gmtii/Prototipo-R820T2/r820t2/r820t_lib.ino

#define R820T2_I2C_ADDRESS   (0x1A)
#define I2C_DEBUG
/*
   Freq calcs
*/
#define XTAL_FREQ           25000000
#define IF_FREQ             5000000
#define CALIBRATION_LO      88000


uint32_t  r820t_freq   =   126200000;
//uint32_t  r820t_freq   =   739900000; // para qo100


#define R820T2_WRITE_START  5
#define R820T2_NUM_REGS 0x20
#define BUFFER_LENGTH 32

/* initial values from airspy */
/* initial freq @ 128MHz -> ~5MHz IF due to xtal mismatch */
static const uint8_t regs_init_array[R820T2_NUM_REGS] = {
  0x00, 0x00, 0x00, 0x00, 0x00,   /* 00 to 04 */
  /* 05 */ 0x90, // LNA manual gain mode, init to 0
  /* 06 */ 0x80,
  /* 07 */ 0x60,
  /* 08 */ 0x80, // Image Gain Adjustment
  /* 09 */ 0x40, // Image Phase Adjustment
  /* 0A */ 0xA8, // Channel filter [0..3]: 0 = widest, f = narrowest - Optimal. Don't touch!
  /* 0B */ 0x0F, // High pass filter - Optimal. Don't touch!
  /* 0C */ 0x40, // VGA control by code, init at 0
  /* 0D */ 0x63, // LNA AGC settings: [0..3]: Lower threshold; [4..7]: High threshold
  /* 0E */ 0x75,
  /* 0F */ 0x68, // Filter Widest, LDO_5V OFF, clk out ON,
  /* 10 */ 0x7C, // REFDIV = 0
  /* 11 */ 0x83,
  /* 12 */ 0x80,
  /* 13 */ 0x00,
  /* 14 */ 0x0F,
  /* 15 */ 0x00,
  /* 16 */ 0xC0,
  /* 17 */ 0x30,
  /* 18 */ 0x48,
  /* 19 */ 0xCC,
  /* 1A */ 0x60,
  /* 1B */ 0x00,
  /* 1C */ 0x54,
  /* 1D */ 0xAE,
  /* 1E */ 0x0A,
  /* 1F */ 0xC0
};

#define ARRAY_SIZE(arr) (sizeof(arr) / sizeof((arr)[0]))

/*
   Tuner frequency ranges
   Kanged & modified from airspy firmware to include freq for scanning table
   "Copyright (C) 2013 Mauro Carvalho Chehab"
   https://stuff.mit.edu/afs/sipb/contrib/linux/drivers/media/tuners/r820t.c
*/
struct r820t2_freq_range {
  uint16_t freq;
  uint8_t open_d;
  uint8_t rf_mux_ploy;
  uint8_t tf_c;
};
const struct r820t2_freq_range freq_ranges[] = {
  {
    /* 0 MHz */              0,
    /* .open_d = */       0x08, /* low */
    /* .rf_mux_ploy = */  0x02, /* R26[7:6]=0 (LPF)  R26[1:0]=2 (low) */
    /* .tf_c = */         0xDF, /* R27[7:0]  band2,band0 */
  }, {
    /* 50 MHz */            50,
    /* .open_d = */       0x08, /* low */
    /* .rf_mux_ploy = */  0x02, /* R26[7:6]=0 (LPF)  R26[1:0]=2 (low) */
    /* .tf_c = */         0xBE, /* R27[7:0]  band4,band1  */
  }, {
    /* 55 MHz */            55,
    /* .open_d = */       0x08, /* low */
    /* .rf_mux_ploy = */  0x02, /* R26[7:6]=0 (LPF)  R26[1:0]=2 (low) */
    /* .tf_c = */         0x8B, /* R27[7:0]  band7,band4 */
  }, {
    /* 60 MHz */            60,
    /* .open_d = */       0x08, /* low */
    /* .rf_mux_ploy = */  0x02, /* R26[7:6]=0 (LPF)  R26[1:0]=2 (low) */
    /* .tf_c = */         0x7B, /* R27[7:0]  band8,band4 */
  }, {
    /* 65 MHz */            65,
    /* .open_d = */       0x08, /* low */
    /* .rf_mux_ploy = */  0x02, /* R26[7:6]=0 (LPF)  R26[1:0]=2 (low) */
    /* .tf_c = */         0x69, /* R27[7:0]  band9,band6 */
  }, {
    /* 70 MHz */            70,
    /* .open_d = */       0x08, /* low */
    /* .rf_mux_ploy = */  0x02, /* R26[7:6]=0 (LPF)  R26[1:0]=2 (low) */
    /* .tf_c = */         0x58, /* R27[7:0]  band10,band7 */
  }, {
    /* 75 MHz */            75,
    /* .open_d = */       0x00, /* high */
    /* .rf_mux_ploy = */  0x02, /* R26[7:6]=0 (LPF)  R26[1:0]=2 (low) */
    /* .tf_c = */         0x44, /* R27[7:0]  band11,band11 */
  }, {
    /* 80 MHz */            80,
    /* .open_d = */       0x00, /* high */
    /* .rf_mux_ploy = */  0x02, /* R26[7:6]=0 (LPF)  R26[1:0]=2 (low) */
    /* .tf_c = */         0x44, /* R27[7:0]  band11,band11 */
  }, {
    /* 90 MHz */            90,
    /* .open_d = */       0x00, /* high */
    /* .rf_mux_ploy = */  0x02, /* R26[7:6]=0 (LPF)  R26[1:0]=2 (low) */
    /* .tf_c = */         0x34, /* R27[7:0]  band12,band11 */
  }, {
    /* 100 MHz */          100,
    /* .open_d = */       0x00, /* high */
    /* .rf_mux_ploy = */  0x02, /* R26[7:6]=0 (LPF)  R26[1:0]=2 (low) */
    /* .tf_c = */         0x34, /* R27[7:0]  band12,band11 */
  }, {
    /* 110 MHz */          110,
    /* .open_d = */       0x00, /* high */
    /* .rf_mux_ploy = */  0x02, /* R26[7:6]=0 (LPF)  R26[1:0]=2 (low) */
    /* .tf_c = */         0x24, /* R27[7:0]  band13,band11 */
  }, {
    /* 120 MHz */          120,
    /* .open_d = */       0x00, /* high */
    /* .rf_mux_ploy = */  0x02, /* R26[7:6]=0 (LPF)  R26[1:0]=2 (low) */
    /* .tf_c = */         0x24, /* R27[7:0]  band13,band11 */
  }, {
    /* 140 MHz */          140,
    /* .open_d = */       0x00, /* high */
    /* .rf_mux_ploy = */  0x02, /* R26[7:6]=0 (LPF)  R26[1:0]=2 (low) */
    /* .tf_c = */         0x14, /* R27[7:0]  band14,band11 */
  }, {
    /* 180 MHz */          180,
    /* .open_d = */       0x00, /* high */
    /* .rf_mux_ploy = */  0x02, /* R26[7:6]=0 (LPF)  R26[1:0]=2 (low) */
    /* .tf_c = */         0x13, /* R27[7:0]  band14,band12 */
  }, {
    /* 220 MHz */          220,
    /* .open_d = */       0x00, /* high */
    /* .rf_mux_ploy = */  0x02, /* R26[7:6]=0 (LPF)  R26[1:0]=2 (low) */
    /* .tf_c = */         0x13, /* R27[7:0]  band14,band12 */
  }, {
    /* 250 MHz */          250,
    /* .open_d = */       0x00, /* high */
    /* .rf_mux_ploy = */  0x02, /* R26[7:6]=0 (LPF)  R26[1:0]=2 (low) */
    /* .tf_c = */         0x11, /* R27[7:0]  highest,highest */
  }, {
    /* 280 MHz */          280,
    /* .open_d = */       0x00, /* high */
    /* .rf_mux_ploy = */  0x02, /* R26[7:6]=0 (LPF)  R26[1:0]=2 (low) */
    /* .tf_c = */         0x00, /* R27[7:0]  highest,highest */
  }, {
    /* 310 MHz */          310,
    /* .open_d = */       0x00, /* high */
    /* .rf_mux_ploy = */  0x41, /* R26[7:6]=1 (bypass)  R26[1:0]=1 (middle) */
    /* .tf_c = */         0x00, /* R27[7:0]  highest,highest */
  }, {
    /* 450 MHz */          450,
    /* .open_d = */       0x00, /* high */
    /* .rf_mux_ploy = */  0x41, /* R26[7:6]=1 (bypass)  R26[1:0]=1 (middle) */
    /* .tf_c = */         0x00, /* R27[7:0]  highest,highest */
  }, {
    /* 588 MHz */          588,
    /* .open_d = */       0x00, /* high */
    /* .rf_mux_ploy = */  0x40, /* R26[7:6]=1 (bypass)  R26[1:0]=0 (highest) */
    /* .tf_c = */         0x00, /* R27[7:0]  highest,highest */
  }, {
    /* 650 MHz */          650,
    /* .open_d = */       0x00, /* high */
    /* .rf_mux_ploy = */  0x40, /* R26[7:6]=1 (bypass)  R26[1:0]=0 (highest) */
    /* .tf_c = */         0x00, /* R27[7:0]  highest,highest */
  }
};



// Cached register values are used in R820T2_write_cache_mask
uint8_t regs_cache[R820T2_NUM_REGS];

// Note: apparently R820T2 allows to read only from address 0x00
void R820T2_read(uint8_t addr, uint8_t *data, uint8_t num) {
  static const uint8_t reverse_table[] = {
    0x0, 0x8, 0x4, 0xC, 0x2, 0xA, 0x6, 0xE,
    0x1, 0x9, 0x5, 0xD, 0x3, 0xB, 0x7, 0xF
  };
  uint16_t timeout = 1000;
  int8_t count = 0;
  uint32_t t1 = millis();
#ifdef I2C_DEBUG
  Serial.print("I2C (0x");
  Serial.print(R820T2_I2C_ADDRESS, HEX);
  Serial.print(") reading ");
  Serial.print(num, DEC);
  Serial.print(" bytes from 0x");
  Serial.print(addr, HEX);
  Serial.print("...");
#endif

  // I2C/TWI subsystem uses internal buffer that breaks with large data requests
  // so if user requests more than BUFFER_LENGTH bytes, we have to do it in
  // smaller chunks instead of all at once
  for (uint8_t k = 0; k < num; k += min((int)num, BUFFER_LENGTH)) {
    Wire.beginTransmission(R820T2_I2C_ADDRESS);
    Wire.write(addr);
    Wire.endTransmission();
    Wire.beginTransmission(R820T2_I2C_ADDRESS);
    Wire.requestFrom(R820T2_I2C_ADDRESS, (uint8_t)min(num - k, BUFFER_LENGTH));

    for (; Wire.available() && (timeout == 0 || millis() - t1 < timeout); count++) {
      data[count] = Wire.read();
#ifdef I2C_DEBUG
      Serial.print(data[count], HEX);
      if (count + 1 < num) Serial.print(" ");
#endif

      // During reading bits are transfered in reverse order,
      // thus we have to restore original bit order.
      for (uint16_t i = 0; i < num; i++) {
        uint16_t val = data[i];
        data[i] = (reverse_table[val & 0xF] << 4) | reverse_table[val >> 4];
      }
    }
    // check for timeout
    if (timeout > 0 && millis() - t1 >= timeout && count < num) count = -1; // timeout

#ifdef I2C_DEBUG
    Serial.print(". Done (");
    Serial.print(count, DEC);
    Serial.println(" read).");
#endif

    //return count;

  }
}
void R820T2_write(uint8_t addr, uint8_t *data, uint8_t num) {
#ifdef I2C_DEBUG
  Serial.print("I2C (0x");
  Serial.print(R820T2_I2C_ADDRESS, HEX);
  Serial.print(") writing ");
  Serial.print(num, DEC);
  Serial.print(" bytes to 0x");
  Serial.print(addr, HEX);
  Serial.print("...");
#endif
  uint8_t status = 0;
  Wire.beginTransmission(R820T2_I2C_ADDRESS);
  Wire.write((uint8_t) addr);
  for (uint8_t i = 0; i < num; i++) {
    Wire.write((uint8_t) data[i]);
#ifdef I2C_DEBUG
    Serial.print(data[i], HEX);
    if (i + 1 < num) Serial.print(" ");
#endif
  }
  status = Wire.endTransmission();
#ifdef I2C_DEBUG
  Serial.print(". Done.");
  Serial.print(". Status = ");
  Serial.println(status);
#endif
  //return status == 0;
}

uint8_t R820T2_read_reg(uint8_t n) {
  if (n >= R820T2_NUM_REGS)
    return 0;

  uint8_t regs[R820T2_NUM_REGS];
  R820T2_read(0x00, regs, sizeof(regs));
  return regs[n];
}

void R820T2_write_reg(uint8_t n, uint8_t data) {
  if (n >= R820T2_NUM_REGS)
    return;
  regs_cache[n] = data;
  R820T2_write(n, &regs_cache[n], 1);
}

/*
   Write single R820T2 reg via I2C with mask vs cached
*/
void R820T2_write_cache_mask(uint8_t reg, uint8_t data, uint8_t mask) {
  /* check for legal reg */
  if (reg >= R820T2_NUM_REGS)
    return;

  /* mask vs cached reg */
  data = (data & mask) | (regs_cache[reg] & ~mask);
  regs_cache[reg] = data;

  /* send via I2C */
  R820T2_write(reg, &regs_cache[reg], 1);
}

/*
   Update Tracking Filter
   Kanged & Modified from airspy firmware

   "inspired by Mauro Carvalho Chehab set_mux technique"
   https://stuff.mit.edu/afs/sipb/contrib/linux/drivers/media/tuners/r820t.c
   part of r820t_set_mux() (set tracking filter)
*/
static void R820T2_set_tf(uint32_t freq) {
  const struct r820t2_freq_range *range;
  unsigned int i;

  /* Get Freq in MHz */
  freq = (uint32_t)((uint64_t)freq * 4295 >> 32); // fast approach

  /* Scan array for proper range */
  for (i = 0; i < ARRAY_SIZE(freq_ranges) - 1; i++) {
    if (freq < freq_ranges[i + 1].freq)

      break;

  }

  range = &freq_ranges[i];
  /* Open Drain */
  R820T2_write_cache_mask(0x17, range->open_d, 0x08);

  /* RF_MUX,Polymux */
  R820T2_write_cache_mask(0x1A, range->rf_mux_ploy, 0xC3);

  /* TF BAND */
  R820T2_write_reg(0x1B, range->tf_c);

  /* XTAL CAP & Drive */
  R820T2_write_cache_mask(0x10, 0x08, 0x0b);

  R820T2_write_cache_mask(0x08, 0x00, 0x3F);

  R820T2_write_cache_mask(0x09, 0x00, 0x3F);
}

/*
   Update LO PLL
*/
void R820T2_set_pll(uint32_t freq) {
  const uint32_t vco_min = 1760000000;
  const uint32_t vco_max = 3900000000;
  uint32_t pll_ref = (XTAL_FREQ >> 1);
  uint32_t pll_ref_2x = XTAL_FREQ;

  uint32_t vco_exact;
  uint32_t vco_frac;
  uint32_t con_frac;
  uint32_t div_num;
  uint32_t n_sdm;
  uint16_t sdm;
  uint8_t ni;
  uint8_t si;
  uint8_t nint;

  /* Calculate VCO output divider */
  for (div_num = 0; div_num < 5; div_num++) {
    vco_exact = freq << (div_num + 1);
    if (vco_exact >= vco_min && vco_exact <= vco_max) {
      break;
    }
  }

  /* Calculate the integer PLL feedback divider */
  vco_exact = freq << (div_num + 1);
  nint = (uint8_t) ((vco_exact + (pll_ref >> 16)) / pll_ref_2x);
  vco_frac = vco_exact - pll_ref_2x * nint;

  nint -= 13;
  ni = (nint >> 2);
  si = nint - (ni << 2);

  /* Set the vco output divider */
  R820T2_write_cache_mask(0x10, (uint8_t) (div_num << 5), 0xE0);

  /* Set the PLL Feedback integer divider */
  R820T2_write_reg(0x14, (uint8_t) (ni + (si << 6)));

  /* Update Fractional PLL */
  if (vco_frac == 0) {
    /* Disable frac pll */
    R820T2_write_cache_mask(0x12, 0x08, 0x08);
  } else {
    /* Compute the Sigma-Delta Modulator */
    vco_frac += pll_ref >> 16;
    sdm = 0;
    for (n_sdm = 0; n_sdm < 16; n_sdm++) {
      con_frac = pll_ref >> n_sdm;
      if (vco_frac >= con_frac) {
        sdm |= (uint16_t) (0x8000 >> n_sdm);
        vco_frac -= con_frac;
        if (vco_frac == 0)
          break;
      }
    }

    /* Update Sigma-Delta Modulator */
    R820T2_write_reg(0x15, (uint8_t)(sdm & 0xFF));
    R820T2_write_reg(0x16, (uint8_t)(sdm >> 8));

    /* Enable frac pll */
    R820T2_write_cache_mask(0x12, 0x00, 0x08);
  }
}

/*
   Update Tracking Filter and LO to frequency
*/
void R820T2_set_frequency(uint32_t freq) {
  r820t_freq = freq;//update frequency cat
  R820T2_set_tf(freq);
  R820T2_set_pll(freq + IF_FREQ);
}

/*
   Set IF Bandwidth [0-15]
*/
void R820T2_set_bandwidth(uint8_t bw) {
  //  const uint8_t modes[] = { 0xE0, 0x80, 0x60, 0x00 };
  //  uint8_t a = 0xB0 | (0x0F - (bw & 0x0F));
  //  uint8_t b = 0x0F | modes[(bw & 0x3) >> 4];
  //  R820T2_write_reg(0x0A, a);
  //  R820T2_write_reg(0x0B, b);

  const uint8_t modes[] = { 0xE0, 0x80, 0x60, 0x00 };
  const uint8_t opt[] = { 15, 14, 13, 12, 11, 10, 9, 8, 7, 6, 5, 4, 3, 2, 1, 0 };
  uint8_t a = 0xB0 | opt[bw & 0x0F];
  uint8_t b = 0x0F | modes[bw >> 4];
  R820T2_write_reg(0x0A, a);
  R820T2_write_reg(0x0B, b);
}

/*
   Set gain of LNA [0-15]
*/
void R820T2_set_lna_gain(uint8_t gain_index) {
  R820T2_write_cache_mask(0x05, gain_index, 0x0F);
}

/*
   Set gain of mixer [0-15]
*/
void R820T2_set_mixer_gain(uint8_t gain_index) {
  R820T2_write_cache_mask(0x07, gain_index, 0x0F);
}

/*
   Set gain of VGA [0-15]
*/
void R820T2_set_vga_gain(uint8_t gain_index) {
  R820T2_write_cache_mask(0x0C, gain_index, 0x0F);
}

/*
   Enable/Disable LNA AGC [0 / 1]
*/
void R820T2_set_lna_agc(uint8_t value) {
  value = value != 0 ? 0x00 : 0x10;
  R820T2_write_cache_mask(0x05, value, 0x10);
}

/*
   Enable/Disable Mixer AGC [0 / 1]
*/
void R820T2_set_mixer_agc(uint8_t value) {
  value = value != 0 ? 0x10 : 0x00;
  R820T2_write_cache_mask(0x07, value, 0x10);
}

/*
   Calibrate
   Kanged from airspy firmware
   "inspired by Mauro Carvalho Chehab calibration technique"
   https://stuff.mit.edu/afs/sipb/contrib/linux/drivers/media/tuners/r820t.c
*/

int32_t R820T2_calibrate() {
  int32_t i, cal_code;

  for (i = 0; i < 5; i++) {
    /* Set filt_cap */
    R820T2_write_cache_mask(0x0B, 0x08, 0x60);

    /* set cali clk =on */
    R820T2_write_cache_mask(0x0F, 0x04, 0x04);

    /* X'tal cap 0pF for PLL */
    R820T2_write_cache_mask(0x10, 0x00, 0x03);

    /* freq used for calibration */
    R820T2_set_pll(CALIBRATION_LO * 1000);

    /* Start Trigger */
    R820T2_write_cache_mask(0x0B, 0x10, 0x10);

    delay(2);

    /* Stop Trigger */
    R820T2_write_cache_mask(0x0B, 0x00, 0x10);

    /* set cali clk =off */
    R820T2_write_cache_mask(0x0F, 0x00, 0x04);

    /* Check if calibration worked */
    cal_code = R820T2_read_reg(0x04) & 0x0F;
    if (cal_code && cal_code != 0x0F)
      return 0;
  }

  /* cal failed */
  return -1;

}

int r820t_standby(void)
{
  R820T2_write_reg(0x05, 0xA0);
  R820T2_write_reg(0x06, 0xD0);
  R820T2_write_reg(0x07, 0x00);
  R820T2_write_reg(0x08, 0x40);
  R820T2_write_reg(0x09, 0xC0);
  R820T2_write_reg(0x0a, 0x70);
  R820T2_write_reg(0x0c, 0xA0);
  R820T2_write_reg(0x0f, 0x2A);
  R820T2_write_reg(0x11, 0x03);
  R820T2_write_reg(0x17, 0xF4);
  R820T2_write_reg(0x19, 0x0C);

  return 0;
}

/*
   Initialize the R820T2
*/
void R820T2_init() {

  byte error;

  Wire.beginTransmission(R820T2_I2C_ADDRESS);
  error = Wire.endTransmission();

  if (error == 0)
  {
    //u8x8.setCursor(0, 5);
    //u8x8.print("OK! R820T found!");

    for (uint8_t i = R820T2_WRITE_START; i < R820T2_NUM_REGS; i++) {
      // R820T2_write_reg is used instead of R820T2_write
      // to initialize regs_cache properly
      R820T2_write_reg(i, regs_init_array[i]);
    }

    /* Calibrate */
    R820T2_calibrate();

    /* set freq after calibrate */
    //R820T2_set_mixer_agc(0);
    //R820T2_set_lna_agc(0);

    R820T2_set_mixer_gain(15);
    //R820T2_set_bandwidth(10);
    R820T2_set_vga_gain(1);
    //R820T2_set_lna_gain(15);

    R820T2_set_frequency(r820t_freq);

    R820T2_set_lna_gain(14);
    //R820T2_set_lna_agc(0x01);
  }
  else
  {
    Serial.println("Unknown error: R820T2 !!!!");
    //u8x8.setCursor(0, 5);
    //u8x8.print("R820T not found!");

    while (1)
    {
      digitalWrite(ledPin, HIGH);
      delay(100);
      digitalWrite(ledPin, LOW);
      delay(100);
    }

  }
}

static const int r82xx_vga_gain_steps[]  = {
  0, 26, 26, 30, 42, 35, 24, 13, 14, 32, 36, 34, 35, 37, 35, 36
};

static const int r82xx_lna_gain_steps[]  = {
  0, 9, 13, 40, 38, 13, 31, 22, 26, 31, 26, 14, 19, 5, 35, 13
};

static const int r82xx_mixer_gain_steps[]  = {
  0, 5, 10, 10, 19, 9, 10, 25, 17, 10, 8, 16, 13, 6, 3, -8
};

int r82xx_set_gain(int set_manual_gain, int gain)
{
  if (set_manual_gain) {
    int i, total_gain = 0;
    uint8_t mix_index = 0, lna_index = 0;
    uint8_t data[4];

    /* LNA auto off */
    R820T2_write_cache_mask( 0x05, 0x10, 0x10);

    /* Mixer auto off */
    R820T2_write_cache_mask( 0x07, 0, 0x10);

    R820T2_read( 0x00, data, sizeof(data));

    /* set fixed VGA gain for now (16.3 dB) */
    R820T2_write_cache_mask( 0x0c, 0x08, 0x9f); //init val 0x08 0x0c works well at 1.7

    for (i = 0; i < 15; i++) {
      if (total_gain >= gain)
        break;

      total_gain += r82xx_lna_gain_steps[++lna_index];

      if (total_gain >= gain)
        break;

      total_gain += r82xx_mixer_gain_steps[++mix_index];
    }

    /* set LNA gain */
    R820T2_write_cache_mask( 0x05, lna_index, 0x0f);

    /* set Mixer gain */
    R820T2_write_cache_mask( 0x07, mix_index, 0x0f);
  } else {
    /* LNA */
    R820T2_write_cache_mask( 0x05, 0, 0x10);

    /* Mixer */
    R820T2_write_cache_mask( 0x07, 0x10, 0x10);

    /* set fixed VGA gain for now (26.5 dB) */
    R820T2_write_cache_mask( 0x0c, 0x0b, 0x9f);

  }

  return 0;
}
